MikhaelKaa/zx_cartridge/media/20260320_191519.jpg

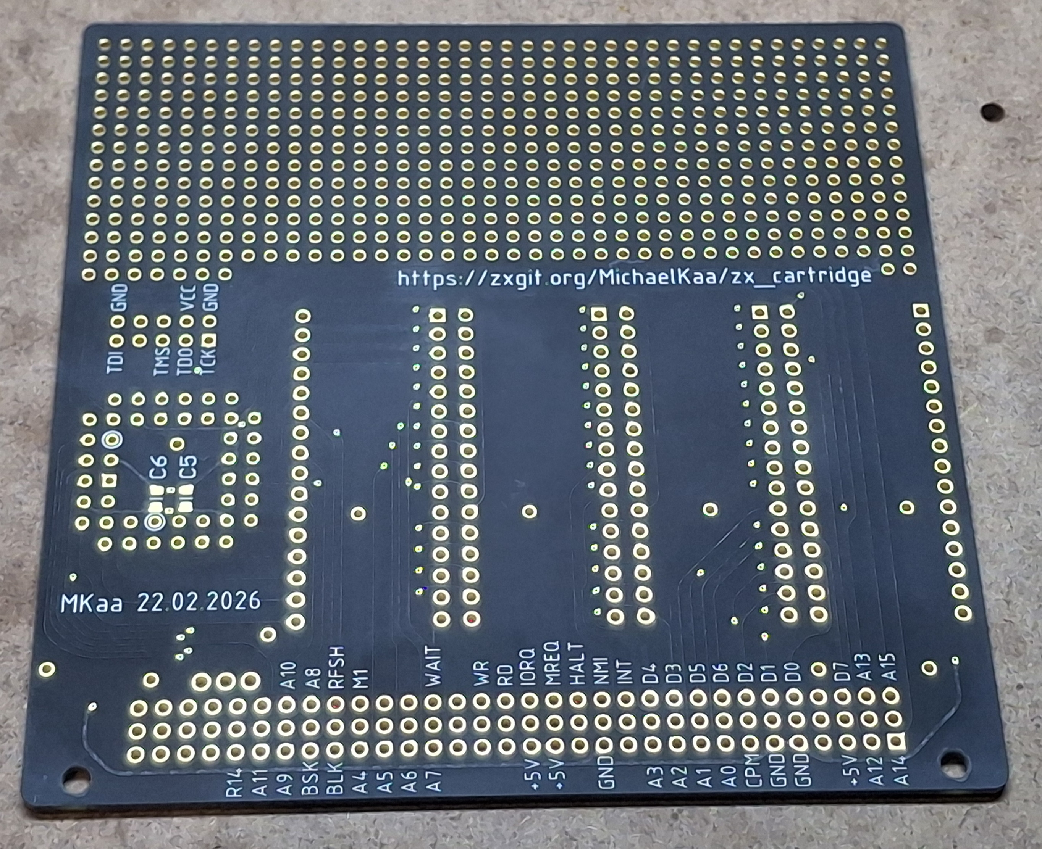
media/20260320_191519.jpg
