MikhaelKaa/zx_cartridge/media/20260320_191531.jpg

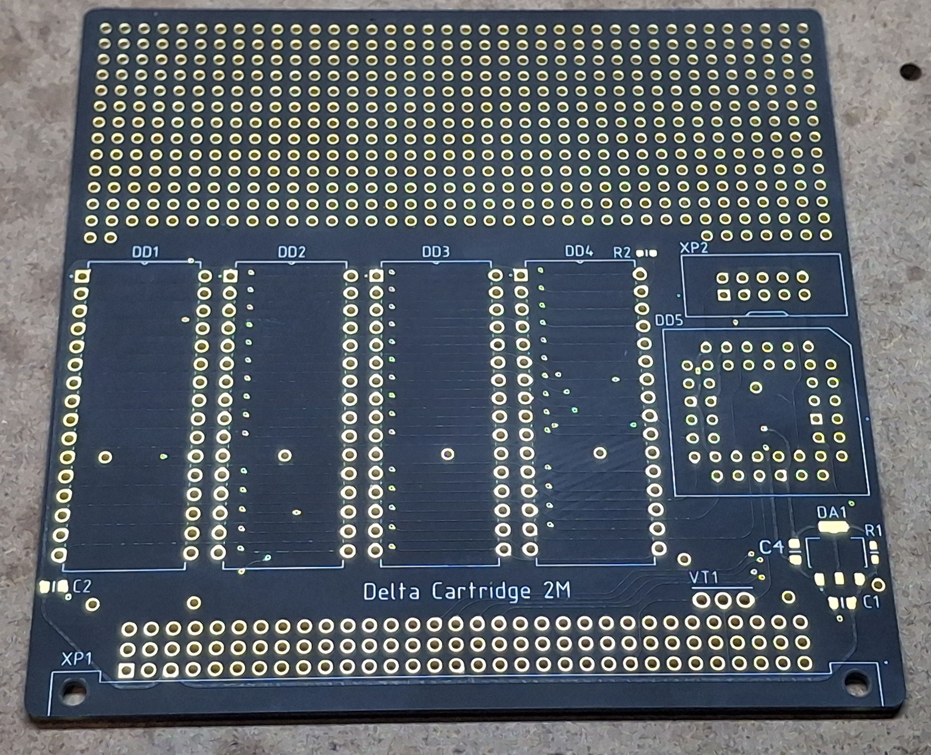
media/20260320_191531.jpg
